JohSchneider/piboy-zero/misc/kicad_generated_2016-02-13/pcb_render_back.png

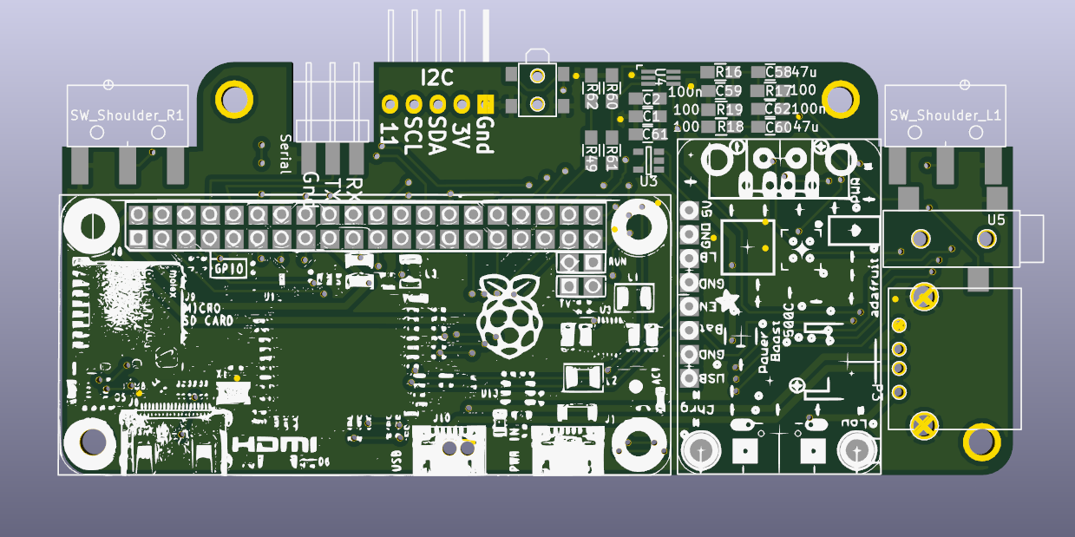
misc/kicad_generated_2016-02-13/pcb_render_back.png
