JohSchneider/piboy-zero/misc/kicad_generated_2016-02-13/pcb_render_front.png

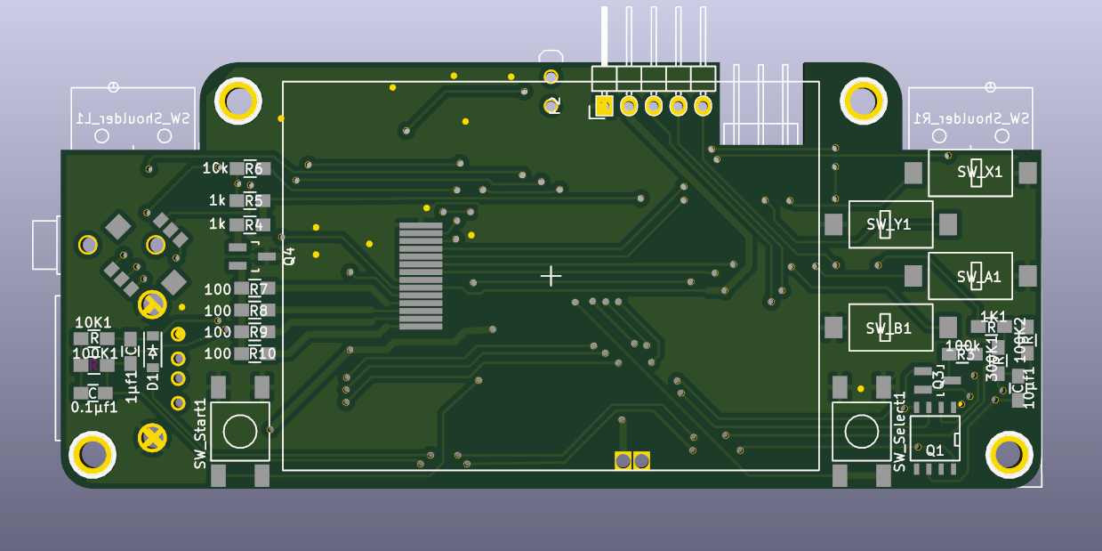
misc/kicad_generated_2016-02-13/pcb_render_front.png
