JohSchneider/piboy-zero/misc/kicad_generated_2016-03-05/raspberry_back.png

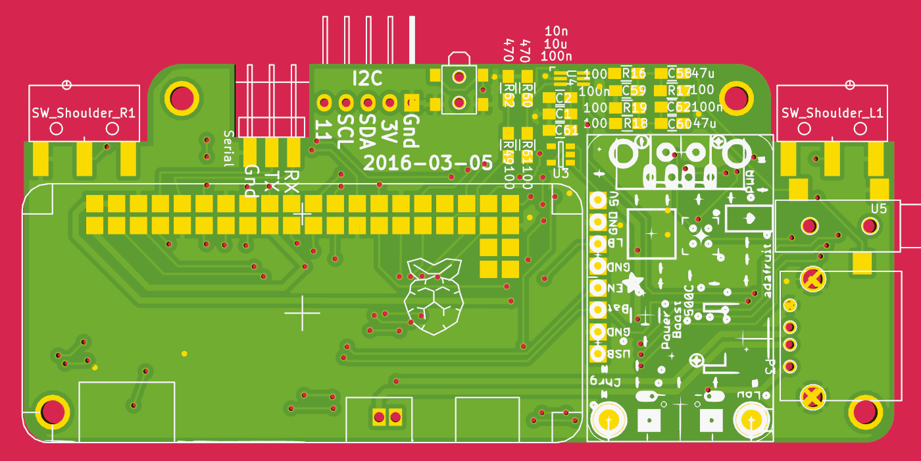
misc/kicad_generated_2016-03-05/raspberry_back.png
