JohSchneider/piboy-zero/misc/kicad_generated_2016-03-05/raspberry_front.png

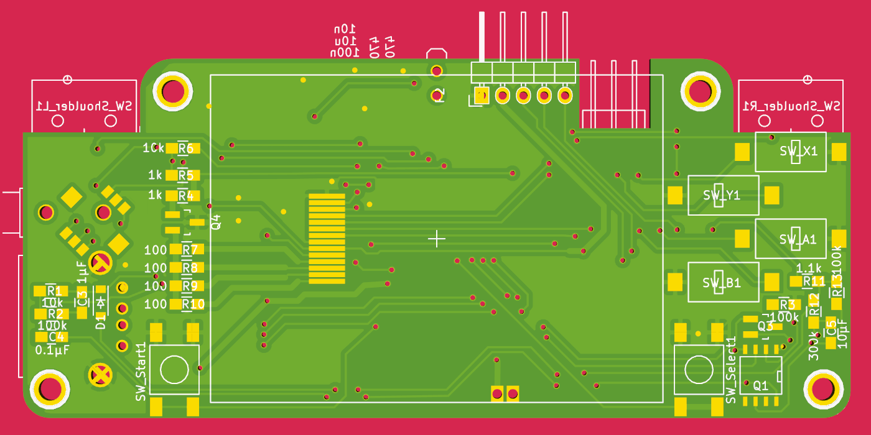
misc/kicad_generated_2016-03-05/raspberry_front.png
