JohSchneider/piboy-zero/misc/kicad_generated_2016-03-13/2016-03-13_back.png

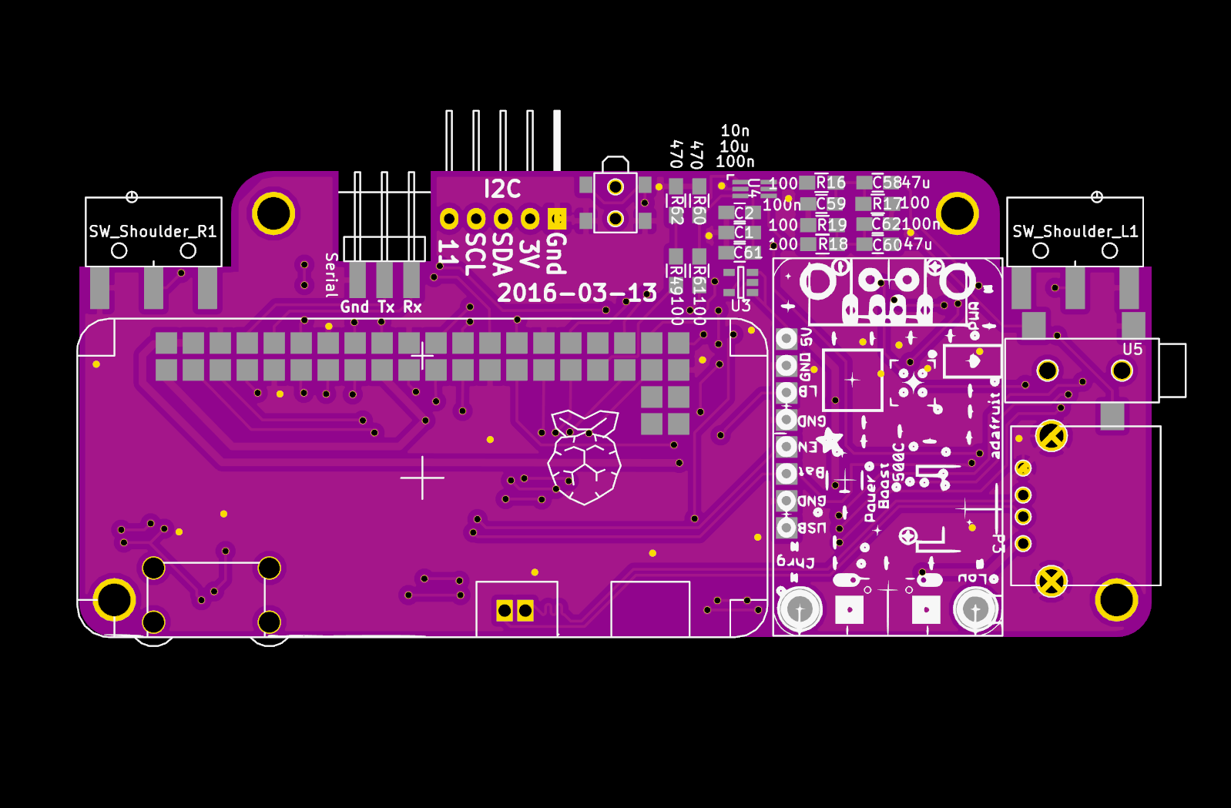
misc/kicad_generated_2016-03-13/2016-03-13_back.png
