JohSchneider/piboy-zero/misc/kicad_generated_2016-03-13/piboy_front.png

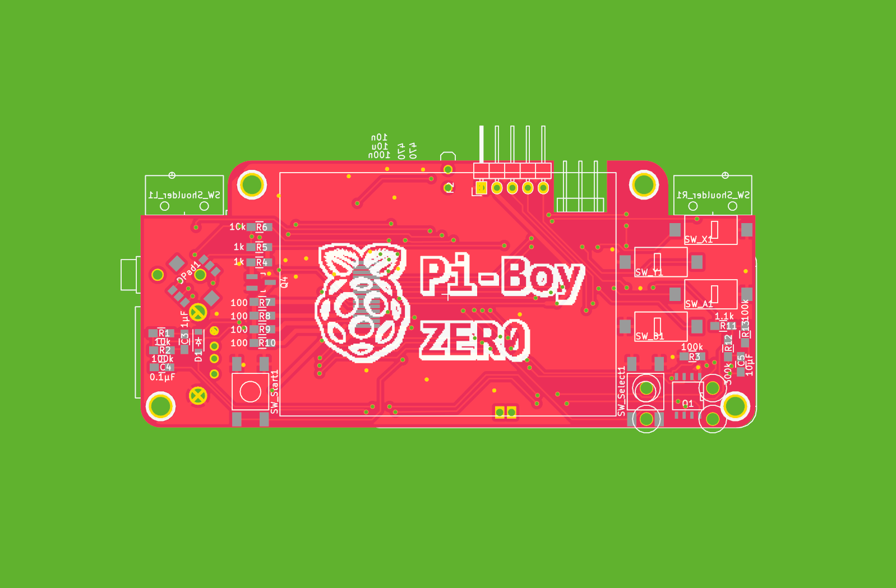
misc/kicad_generated_2016-03-13/piboy_front.png
