JohSchneider/piboy-zero/misc/kicad_generated_2016-03-13/piggrl_zero_baseboard_front_2016-03-13.png

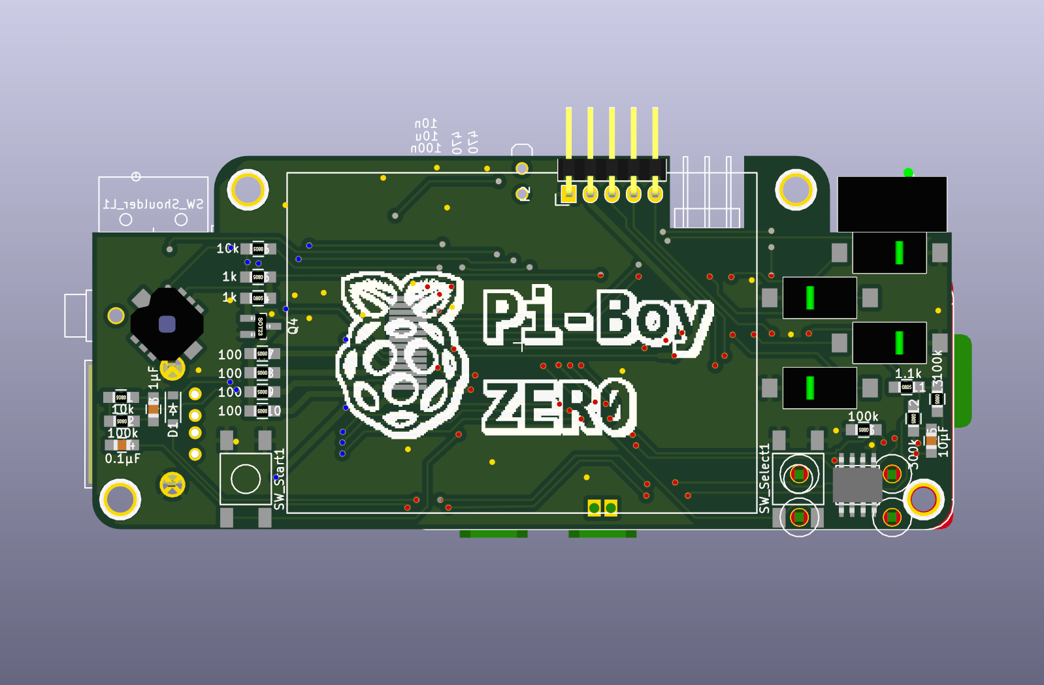
misc/kicad_generated_2016-03-13/piggrl_zero_baseboard_front_2016-03-13.png
