JohSchneider/piboy-zero/software/retropie-config/emulationstation/themes/minimal/retropie/art/raspberryA+.png

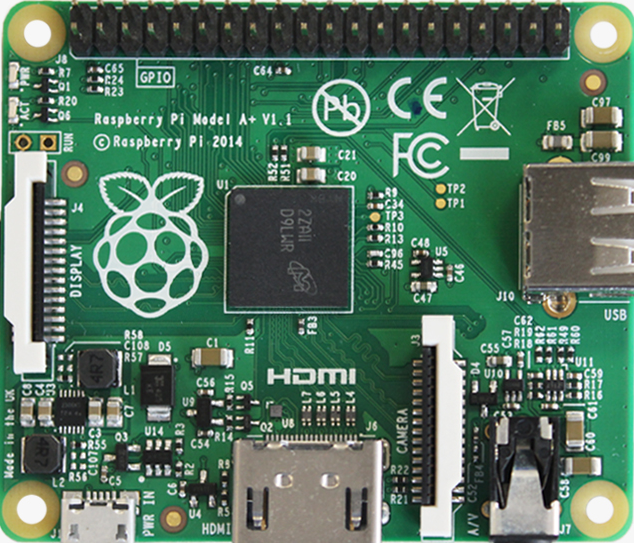
software/retropie-config/emulationstation/themes/minimal/retropie/art/raspberryA+.png
