JohSchneider/piboy-zero/software/retropie-config/emulationstation/themes/minimal/retropie/art/raspberryA+_blur.png

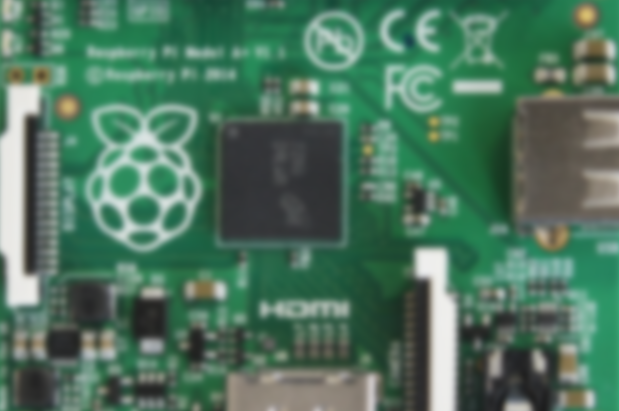
software/retropie-config/emulationstation/themes/minimal/retropie/art/raspberryA+_blur.png
