JohSchneider/piboy-zero/enclosure/button_shoulder.stl

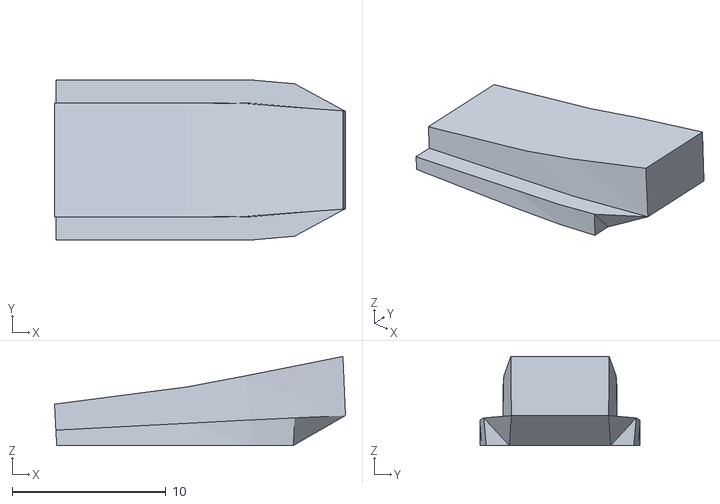
[picture p30: CAD file, 2016-04-09]
enclosure/button_shoulder.stl
18.9 x 10.4 x 5.79
