JohSchneider/piboy-zero/misc/kicad_generated_2016-03-05/solder-n-test_2_audio_back.png

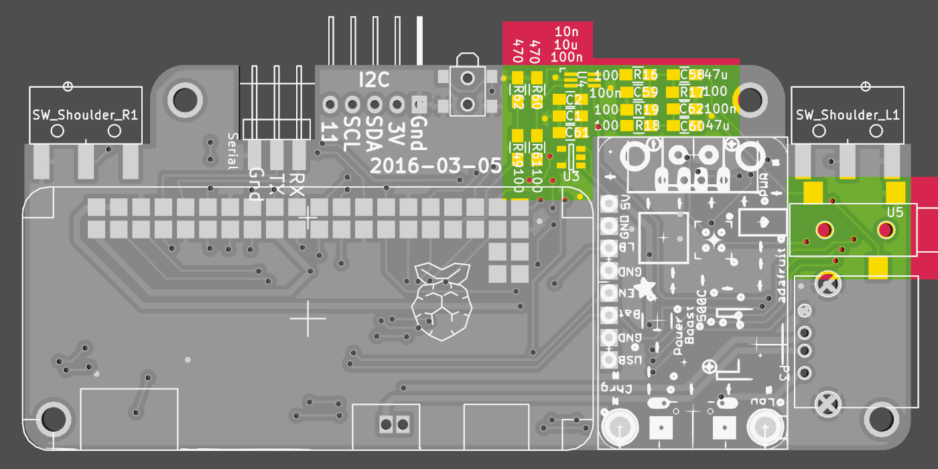
misc/kicad_generated_2016-03-05/solder-n-test_2_audio_back.png
