JohSchneider/piboy-zero/software/retropie-config/emulationstation/themes/minimal/art/test.jpg

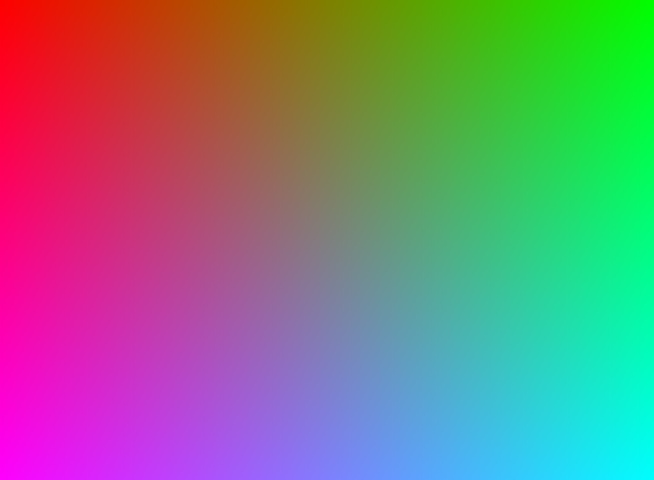
software/retropie-config/emulationstation/themes/minimal/art/test.jpg
